cptnpopcorn/doorlock/common/libdesfire/AES128.cpp

/* 
 * Description: Implementation of the AES-128 as defined by the FIPS PUB 197: 
 * The official AES standard
 *  
 * COPYRIGHT: BSD 
 * 
 * Copyright (c) 2011, Texas Instruments Incorporated
 * All rights reserved.
 * 
 * Converted from C to C++ by Elmü 2016
 *
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
 * *  Redistributions of source code must retain the above copyright
 *    notice, this list of conditions and the following disclaimer.
 *
 * *  Redistributions in binary form must reproduce the above copyright
 *    notice, this list of conditions and the following disclaimer in the
 *    documentation and/or other materials provided with the distribution.
 *
 * *  Neither the name of Texas Instruments Incorporated nor the names of
 *    its contributors may be used to endorse or promote products derived
 *    from this software without specific prior written permission.
 *
 * THIS SOFTWARE IS PROVIDED BY THE COPYRIGHT HOLDERS AND CONTRIBUTORS "AS IS"
 * AND ANY EXPRESS OR IMPLIED WARRANTIES, INCLUDING, BUT NOT LIMITED TO,
 * THE IMPLIED WARRANTIES OF MERCHANTABILITY AND FITNESS FOR A PARTICULAR
 * PURPOSE ARE DISCLAIMED. IN NO EVENT SHALL THE COPYRIGHT OWNER OR
 * CONTRIBUTORS BE LIABLE FOR ANY DIRECT, INDIRECT, INCIDENTAL, SPECIAL,
 * EXEMPLARY, OR CONSEQUENTIAL DAMAGES (INCLUDING, BUT NOT LIMITED TO,
 * PROCUREMENT OF SUBSTITUTE GOODS OR SERVICES; LOSS OF USE, DATA, OR PROFITS;
 * OR BUSINESS INTERRUPTION) HOWEVER CAUSED AND ON ANY THEORY OF LIABILITY,
 * WHETHER IN CONTRACT, STRICT LIABILITY, OR TORT (INCLUDING NEGLIGENCE OR
 * OTHERWISE) ARISING IN ANY WAY OUT OF THE USE OF THIS SOFTWARE,
 * EVEN IF ADVISED OF THE POSSIBILITY OF SUCH DAMAGE.
 * --/COPYRIGHT--*/
/*
 * TI_aes_128.c
 *
 *  Created on: Nov 3, 2011
 *      Author: Eric Peeters
 */

#include "AES128.h"
#include "Utils.h"
 
// foreward sbox
const unsigned char sbox[256] =   {
//0     1    2      3     4    5     6     7      8    9     A      B    C     D     E     F
0x63, 0x7c, 0x77, 0x7b, 0xf2, 0x6b, 0x6f, 0xc5, 0x30, 0x01, 0x67, 0x2b, 0xfe, 0xd7, 0xab, 0x76, //0
0xca, 0x82, 0xc9, 0x7d, 0xfa, 0x59, 0x47, 0xf0, 0xad, 0xd4, 0xa2, 0xaf, 0x9c, 0xa4, 0x72, 0xc0, //1
0xb7, 0xfd, 0x93, 0x26, 0x36, 0x3f, 0xf7, 0xcc, 0x34, 0xa5, 0xe5, 0xf1, 0x71, 0xd8, 0x31, 0x15, //2
0x04, 0xc7, 0x23, 0xc3, 0x18, 0x96, 0x05, 0x9a, 0x07, 0x12, 0x80, 0xe2, 0xeb, 0x27, 0xb2, 0x75, //3
0x09, 0x83, 0x2c, 0x1a, 0x1b, 0x6e, 0x5a, 0xa0, 0x52, 0x3b, 0xd6, 0xb3, 0x29, 0xe3, 0x2f, 0x84, //4
0x53, 0xd1, 0x00, 0xed, 0x20, 0xfc, 0xb1, 0x5b, 0x6a, 0xcb, 0xbe, 0x39, 0x4a, 0x4c, 0x58, 0xcf, //5
0xd0, 0xef, 0xaa, 0xfb, 0x43, 0x4d, 0x33, 0x85, 0x45, 0xf9, 0x02, 0x7f, 0x50, 0x3c, 0x9f, 0xa8, //6
0x51, 0xa3, 0x40, 0x8f, 0x92, 0x9d, 0x38, 0xf5, 0xbc, 0xb6, 0xda, 0x21, 0x10, 0xff, 0xf3, 0xd2, //7
0xcd, 0x0c, 0x13, 0xec, 0x5f, 0x97, 0x44, 0x17, 0xc4, 0xa7, 0x7e, 0x3d, 0x64, 0x5d, 0x19, 0x73, //8
0x60, 0x81, 0x4f, 0xdc, 0x22, 0x2a, 0x90, 0x88, 0x46, 0xee, 0xb8, 0x14, 0xde, 0x5e, 0x0b, 0xdb, //9
0xe0, 0x32, 0x3a, 0x0a, 0x49, 0x06, 0x24, 0x5c, 0xc2, 0xd3, 0xac, 0x62, 0x91, 0x95, 0xe4, 0x79, //A
0xe7, 0xc8, 0x37, 0x6d, 0x8d, 0xd5, 0x4e, 0xa9, 0x6c, 0x56, 0xf4, 0xea, 0x65, 0x7a, 0xae, 0x08, //B
0xba, 0x78, 0x25, 0x2e, 0x1c, 0xa6, 0xb4, 0xc6, 0xe8, 0xdd, 0x74, 0x1f, 0x4b, 0xbd, 0x8b, 0x8a, //C
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
  // cast to signed value
  temp = (signed char) value;
  // if MSB is 1, then this will signed extend and fill the temp variable with 1's
  temp = temp >> 7;
  // AND with the reduction variable
  temp = temp & 0x1b;
  // finally shift and reduce the value
  return ((value << 1)^temp);
}

// ------------------------------------------
// ATTENTION: This function modifies the key!
// ------------------------------------------
// AES encryption and decryption function
// The code was optimized for memory (flash and ram)
// Combining both encryption and decryption resulted in a slower implementation
// but much smaller than the 2 functions separated
// This function only implements AES-128 encryption and decryption (AES-192 and 
// AES-256 are not supported by this code) 
void AES::aes_enc_dec(unsigned char state[16], unsigned char key[16], unsigned char dir)
{
  unsigned char buf1, buf2, buf3, buf4, round, i;
   
  // In case of decryption
  if (dir) {
    // compute the last key of encryption before starting the decryption
    for (round = 0 ; round < 10; round++) {
      //key schedule
      key[0] = sbox[key[13]]^key[0]^Rcon[round];
      key[1] = sbox[key[14]]^key[1];
      key[2] = sbox[key[15]]^key[2];
      key[3] = sbox[key[12]]^key[3];
      for (i=4; i<16; i++) {
        key[i] = key[i] ^ key[i-4];
      }
    }
    
    //first Addroundkey
    for (i = 0; i <16; i++){
      state[i]=state[i] ^ key[i];
    }
  }
  
  // main loop
  for (round = 0; round < 10; round++){
    if (dir){
      //Inverse key schedule
      for (i=15; i>3; --i) {
    key[i] = key[i] ^ key[i-4];
      }  
      key[0] = sbox[key[13]]^key[0]^Rcon[9-round];
      key[1] = sbox[key[14]]^key[1];
      key[2] = sbox[key[15]]^key[2];
      key[3] = sbox[key[12]]^key[3]; 
    } else {
      for (i = 0; i <16; i++){
        // with shiftrow i+5 mod 16
    state[i]=sbox[state[i] ^ key[i]];
      }
      //shift rows
      buf1 = state[1];
      state[1] = state[5];
      state[5] = state[9];
      state[9] = state[13];
      state[13] = buf1;

      buf1 = state[2];
      buf2 = state[6];
      state[2] = state[10];
      state[6] = state[14];
      state[10] = buf1;
      state[14] = buf2;

      buf1 = state[15];
      state[15] = state[11];
      state[11] = state[7];
      state[7] = state[3];
      state[3] = buf1;
    }
    //mixcol - inv mix
    if ((round > 0 && dir) || (round < 9 && !dir)) {
      for (i=0; i <4; i++){
        buf4 = (i << 2);
        if (dir){
          // precompute for decryption
          buf1 = galois_mul2(galois_mul2(state[buf4]^state[buf4+2]));
          buf2 = galois_mul2(galois_mul2(state[buf4+1]^state[buf4+3]));
          state[buf4] ^= buf1; state[buf4+1] ^= buf2; state[buf4+2] ^= buf1; state[buf4+3] ^= buf2; 
        }
        // in all cases
        buf1 = state[buf4] ^ state[buf4+1] ^ state[buf4+2] ^ state[buf4+3];
        buf2 = state[buf4];
        buf3 = state[buf4]^state[buf4+1];   buf3=galois_mul2(buf3); state[buf4]   = state[buf4]   ^ buf3 ^ buf1;
        buf3 = state[buf4+1]^state[buf4+2]; buf3=galois_mul2(buf3); state[buf4+1] = state[buf4+1] ^ buf3 ^ buf1;
        buf3 = state[buf4+2]^state[buf4+3]; buf3=galois_mul2(buf3); state[buf4+2] = state[buf4+2] ^ buf3 ^ buf1;
        buf3 = state[buf4+3]^buf2;          buf3=galois_mul2(buf3); state[buf4+3] = state[buf4+3] ^ buf3 ^ buf1;
      }
    }
    
    if (dir) {
      //Inv shift rows
      // Row 1
      buf1 = state[13];
      state[13] = state[9];
      state[9] = state[5];
      state[5] = state[1];
      state[1] = buf1;
      //Row 2
      buf1 = state[10];
      buf2 = state[14];
      state[10] = state[2];
      state[14] = state[6];
      state[2] = buf1;
      state[6] = buf2;
      //Row 3
      buf1 = state[3];
      state[3] = state[7];
      state[7] = state[11];
      state[11] = state[15];
      state[15] = buf1;         
           
      for (i = 0; i <16; i++){
        // with shiftrow i+5 mod 16
        state[i]=rsbox[state[i]] ^ key[i];
      } 
    } else {
      //key schedule
      key[0] = sbox[key[13]]^key[0]^Rcon[round];
      key[1] = sbox[key[14]]^key[1];
      key[2] = sbox[key[15]]^key[2];
      key[3] = sbox[key[12]]^key[3];
      for (i=4; i<16; i++) {
        key[i] = key[i] ^ key[i-4];
      }
    }
  }
  if (!dir) {
  //last Addroundkey
    for (i = 0; i <16; i++){
      // with shiftrow i+5 mod 16
      state[i]=state[i] ^ key[i];
    } // enf for
  } // end if (!dir)
} // end function


// ----------------------------------------------------------------------------------------------
// C++ code added by Elmü
// ----------------------------------------------------------------------------------------------

AES::AES()
{
    ms32_BlockSize = 16; // AES always encrypts blocks of 16 byte independent of the key size
}

AES::~AES()
{
}

// 16 byte key = 128 bit
// It is allowed to pass a larger key than 16 bytes here. In this case only the first 16 bytes will be used.
bool AES::SetKeyData(const uint8_t* u8_Key, int s32_KeySize, uint8_t u8_Version)
{
    if (s32_KeySize < 16)
        return false;

    std::memcpy(mu8_Key, u8_Key, 16);
    ClearIV(); // Fill IV with zeroes
    mu8_Version  = u8_Version;
    ms32_KeySize = 16;
    me_KeyType   = DF_KEY_AES;
    return true;
}

// 1 block = 16 bytes
bool AES::CryptDataBlock(uint8_t* u8_Out, const uint8_t* u8_In, DESFireCipher e_Cipher)
{
    if (ms32_KeySize != 16)
        return false; // Key not set
  
    // aes_enc_dec() modifies the key!
    uint8_t u8_TempKey[16];
    std::memcpy(u8_TempKey, mu8_Key, 16);
  
    std::memcpy(u8_Out, u8_In, 16);
    aes_enc_dec(u8_Out, u8_TempKey, e_Cipher);
    return true;
}
