cptnpopcorn/doorlock/common/libdesfire/PN532.h

#ifndef ADAFRUIT_PN532_H
#define ADAFRUIT_PN532_H

#include "Utils.h"

// The maximum time to wait for an answer from the PN532
// Do NOT use infinite timeouts like in Adafruit code!
#define PN532_TIMEOUT 1000

// The packet buffer is used for sending commands and for receiving responses from the PN532
#define PN532_PACKBUFFSIZE 80

// ----------------------------------------------------------------------

// PN532 Commands
#define PN532_COMMAND_DIAGNOSE (0x00)
#define PN532_COMMAND_GETFIRMWAREVERSION (0x02)
#define PN532_COMMAND_GETGENERALSTATUS (0x04)
#define PN532_COMMAND_READREGISTER (0x06)
#define PN532_COMMAND_WRITEREGISTER (0x08)
#define PN532_COMMAND_READGPIO (0x0C)
#define PN532_COMMAND_WRITEGPIO (0x0E)
#define PN532_COMMAND_SETSERIALBAUDRATE (0x10)
#define PN532_COMMAND_SETPARAMETERS (0x12)
#define PN532_COMMAND_SAMCONFIGURATION (0x14)
#define PN532_COMMAND_POWERDOWN (0x16)
#define PN532_COMMAND_RFCONFIGURATION (0x32)
#define PN532_COMMAND_RFREGULATIONTEST (0x58)
#define PN532_COMMAND_INJUMPFORDEP (0x56)
#define PN532_COMMAND_INJUMPFORPSL (0x46)
#define PN532_COMMAND_INLISTPASSIVETARGET (0x4A)
#define PN532_COMMAND_INATR (0x50)
#define PN532_COMMAND_INPSL (0x4E)
#define PN532_COMMAND_INDATAEXCHANGE (0x40)
#define PN532_COMMAND_INCOMMUNICATETHRU (0x42)
#define PN532_COMMAND_INDESELECT (0x44)
#define PN532_COMMAND_INRELEASE (0x52)
#define PN532_COMMAND_INSELECT (0x54)
#define PN532_COMMAND_INAUTOPOLL (0x60)
#define PN532_COMMAND_TGINITASTARGET (0x8C)
#define PN532_COMMAND_TGSETGENERALBYTES (0x92)
#define PN532_COMMAND_TGGETDATA (0x86)
#define PN532_COMMAND_TGSETDATA (0x8E)
#define PN532_COMMAND_TGSETMETADATA (0x94)
#define PN532_COMMAND_TGGETINITIATORCOMMAND (0x88)
#define PN532_COMMAND_TGRESPONSETOINITIATOR (0x90)
#define PN532_COMMAND_TGGETTARGETSTATUS (0x8A)

#define PN532_WAKEUP (0x55)

#define PN532_SPI_STATUSREAD (0x02)
#define PN532_SPI_DATAWRITE (0x01)
#define PN532_SPI_DATAREAD (0x03)
#define PN532_SPI_READY (0x01)

#define PN532_I2C_ADDRESS (0x48 >> 1)
#define PN532_I2C_READY (0x01)

#define PN532_GPIO_P30 (0x01)
#define PN532_GPIO_P31 (0x02)
#define PN532_GPIO_P32 (0x04)
#define PN532_GPIO_P33 (0x08)
#define PN532_GPIO_P34 (0x10)
#define PN532_GPIO_P35 (0x20)
#define PN532_GPIO_VALIDATIONBIT (0x80)

#define CARD_TYPE_106KB_ISO14443A (0x00) // card baudrate 106 kB
#define CARD_TYPE_212KB_FELICA (0x01)	 // card baudrate 212 kB
#define CARD_TYPE_424KB_FELICA (0x02)	 // card baudrate 424 kB
#define CARD_TYPE_106KB_ISO14443B (0x03) // card baudrate 106 kB
#define CARD_TYPE_106KB_JEWEL (0x04)	 // card baudrate 106 kB

// Prefixes for NDEF Records (to identify record type), not used
#define NDEF_URIPREFIX_NONE (0x00)
#define NDEF_URIPREFIX_HTTP_WWWDOT (0x01)
#define NDEF_URIPREFIX_HTTPS_WWWDOT (0x02)
#define NDEF_URIPREFIX_HTTP (0x03)
#define NDEF_URIPREFIX_HTTPS (0x04)
#define NDEF_URIPREFIX_TEL (0x05)
#define NDEF_URIPREFIX_MAILTO (0x06)
#define NDEF_URIPREFIX_FTP_ANONAT (0x07)
#define NDEF_URIPREFIX_FTP_FTPDOT (0x08)
#define NDEF_URIPREFIX_FTPS (0x09)
#define NDEF_URIPREFIX_SFTP (0x0A)
#define NDEF_URIPREFIX_SMB (0x0B)
#define NDEF_URIPREFIX_NFS (0x0C)
#define NDEF_URIPREFIX_FTP (0x0D)
#define NDEF_URIPREFIX_DAV (0x0E)
#define NDEF_URIPREFIX_NEWS (0x0F)
#define NDEF_URIPREFIX_TELNET (0x10)
#define NDEF_URIPREFIX_IMAP (0x11)
#define NDEF_URIPREFIX_RTSP (0x12)
#define NDEF_URIPREFIX_URN (0x13)
#define NDEF_URIPREFIX_POP (0x14)
#define NDEF_URIPREFIX_SIP (0x15)
#define NDEF_URIPREFIX_SIPS (0x16)
#define NDEF_URIPREFIX_TFTP (0x17)
#define NDEF_URIPREFIX_BTSPP (0x18)
#define NDEF_URIPREFIX_BTL2CAP (0x19)
#define NDEF_URIPREFIX_BTGOEP (0x1A)
#define NDEF_URIPREFIX_TCPOBEX (0x1B)
#define NDEF_URIPREFIX_IRDAOBEX (0x1C)
#define NDEF_URIPREFIX_FILE (0x1D)
#define NDEF_URIPREFIX_URN_EPC_ID (0x1E)
#define NDEF_URIPREFIX_URN_EPC_TAG (0x1F)
#define NDEF_URIPREFIX_URN_EPC_PAT (0x20)
#define NDEF_URIPREFIX_URN_EPC_RAW (0x21)
#define NDEF_URIPREFIX_URN_EPC (0x22)
#define NDEF_URIPREFIX_URN_NFC (0x23)

enum eCardType
{
	CARD_Unknown = 0,	// Mifare Classic or other card
	CARD_Desfire = 1,	// A Desfire card with normal 7 byte UID  (bit 0)
	CARD_DesRandom = 3, // A Desfire card with 4 byte random UID  (bit 0 + 1)
};

class PN532Interface;

class PN532
{
public:
	PN532(PN532Interface&) noexcept;

	// Generic PN532 functions
	void begin();
	void SetDebugLevel(uint8_t level);
	bool SamConfig();
	bool GetFirmwareVersion(uint8_t *pIcType, uint8_t *pVersionHi, uint8_t *pVersionLo, uint8_t *pFlags);
	bool WriteGPIO(bool P30, bool P31, bool P33, bool P35);
	bool SetPassiveActivationRetries();
	bool DeselectCard();
	bool ReleaseCard();
	bool SelectCard();

	// This function is overridden in Desfire.cpp
	virtual bool SwitchOffRfField();

	// ISO14443A functions
	bool ReadPassiveTargetID(uint8_t *uidBuffer, uint8_t *uidLength, eCardType *pe_CardType);

protected:
	// Low Level functions
	bool CheckPN532Status(uint8_t u8_Status);
	bool SendCommandCheckAck(uint8_t *cmd, uint8_t cmdlen);
	uint8_t ReadData(uint8_t *buff, uint8_t len);

	uint8_t mu8_DebugLevel; // 0, 1, or 2
	uint8_t mu8_PacketBuffer[PN532_PACKBUFFSIZE];

private:
	void WriteCommand(uint8_t *cmd, uint8_t cmdlen);
	bool ReadAck();

	PN532Interface& interface;
};

#endif
