cptnpopcorn/doorlock/common/libdesfire/Tfi.h

#ifndef E5212CF3_8B69_4F4E_9EA7_E5E1E561419E
#define E5212CF3_8B69_4F4E_9EA7_E5E1E561419E

#include <cstdint>

enum class Tfi : uint8_t
{	
	InfoFromController = 0xD4,
	InfoToController = 0xD5,
};

#endif /* E5212CF3_8B69_4F4E_9EA7_E5E1E561419E */
